UMaineECE498/LEDGradCap/hardware/led-cap.sch

## KiCad design hardware/led-cap.sch (2015-03-27)

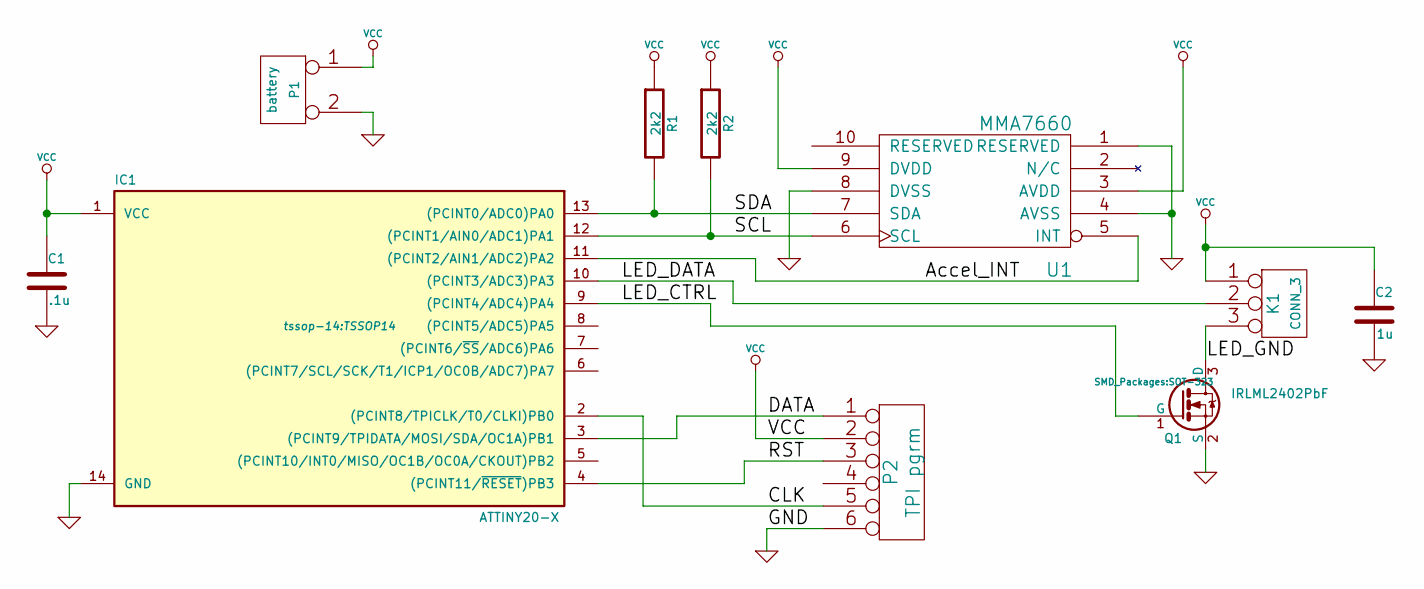
[picture p4: schematic led-cap.sch]

Parts:
C1: .1u; C_0805_HandSoldering
C2: 1u; C_0805_HandSoldering
IC1: ATTINY20-X; TSSOP14
K1: CONN_3; GS3
P1: battery; AA Box
P2: TPI pgrm
Q1: IRLML2402PbF; SOT-323
R1, R2: 2k2; R_0603_HandSoldering
U1: MMA7660; DFN-10

Connections:
Accel_INT: IC1.11 ((PCINT2/AIN1/ADC2)PA2), U1.5 (INT)
CLK: IC1.2 ((PCINT8/TPICLK/T0/CLKI)PB0), P2.5
DATA: IC1.3 ((PCINT9/TPIDATA/MOSI/SDA/OC1A)PB1), P2.1
GND: C1.2, C2.2, IC1.14 (GND), P1.2 (PM), P2.6, Q1.2 (S), U1.1 (RESERVED), U1.4 (AVSS), U1.8 (DVSS)
LED_CTRL: IC1.9 ((PCINT4/ADC4)PA4), Q1.1 (G)
LED_DATA: IC1.10 ((PCINT3/ADC3)PA3), K1.2 (PM)
LED_GND: K1.3, Q1.3 (D)
RST: IC1.4 ((PCINT11/~RESET~)PB3), P2.3
SCL: IC1.12 ((PCINT1/AIN0/ADC1)PA1), R2.2, U1.6 (SCL)
SDA: IC1.13 ((PCINT0/ADC0)PA0), R1.2, U1.7 (SDA)
VCC: C1.1, C2.1, IC1.1 (VCC), K1.1, P1.1, P2.2, R1.1, R2.1, U1.3 (AVDD), U1.9 (DVDD)
