UMaineECE498/LEDGradCap/software/ledRoutines.h

#ifndef __ledRoutines_h__
#define __ledRoutines_h__


#define IN 1        //  Fade directions
#define OUT -1


// Pattern routines

void rgbfade(void);
void bwfade(void);


#endif // __ledRoutines_h__
