UMaineECE498/LEDGradCap/software/system.h

#ifndef __system_h__
#define __system_h__

#include <avr/io.h>

#define LED_DATA_PORT 	PORTA
#define LED_DATA_DIR	DDRA
#define LED_DATA_PIN	PIN3

#define LED_EN_PORT		PORTA
#define LED_EN_DIR		DDRA
#define LED_EN_PIN	PIN4

#define NUM_LEDS	8
#define NUM_FADE_STEPS 64
#define FADE_DELAY 25

extern uint8_t red[8];	// Red values
extern uint8_t green[8];	// Green values
extern uint8_t blue[8];	// Blue values

#endif	// __system_h__
